VMelnalksnis/DCEL-1000/SIMULATION/LTSpice/IXTK102N65 test.asc

M1: nmos; IXTK102N65
R1: res; 2
V1: voltage; 10
V2: voltage; {gs}
Named nets: 0
.lib "D:\\projects\\Electronic-Load\\SIMULATION\\LTSpice\\SPICE Models\\IXTK102N65.lib"
.step param gs list 5 6 7 8 10
.dc V1 0 25 0.1
