VMelnalksnis/DCEL-1000/SIMULATION/LTSpice/_Range Switch.asc

B1: bv; V=(white(2e7*time)/2)
B2: bv; V=(white(2e7*time)/10)
C1: cap; 470n; V=50 Rser=1m Lser=700p
L1: ind; 10n
L2: ind; 10n
L3: ind; 10n
L4: ind; 10n
L5: ind; 10m
M1: nmos; SiRC10DP
M2: nmos; SiRC10DP
Q1: npn; BC817-40
Q2: npn; BC817-40
Q3: pnp; BC807-40
R1: res; 1k
R2: res; 1k
R3: res; 100k
R4: res; 2
R5: res; 2
R6: res; 2
R7: res; 2k15
R8: res; 1.5m
R9: res; 1
V1: voltage; 12
V2: voltage; PULSE(0 5 4m 10n 10n 0.5u 100u)
V3: voltage; 20
Named nets: 0, +12V, BYP, dut+
.lib "D:\\Cloud\\OneDrive\\projects\\DCEL-1000\\SIMULATION\\LTSpice\\SPICE Models\\SiRC10DP_PS_Rev_A.LIB"
.tran 0 5.5m 5m startup uic
