VMelnalksnis/DCEL-1000/SIMULATION/LTSpice/Load Gate.asc

B1: bv; V=(white(2e6*time)/1)
B2: bv; V=(white(2e6*time)/1)
C1: cap; 10n
D1: diode; RFN30TS6D
L1: ind; {ldut}; Rser=10m
L2: ind; 100n; Rser=10m
M1: nmos; IXFX90N30
Q1: npn; BC817-25
Q2: pnp; BC807-25
Q3: pnp; BC807-25
Q4: npn; BC817-25
R1: res; 2
R2: res; 5m
R3: res; 2
R4: res; 10k
R5: res; 10k
R6: res; 10k
R7: res; 10k
R8: res; 10k
R9: res; 10k
R10: res; 10k
R11: res; 10k
R12: res; 10k
R13: res; 10k
R14: res; 5k
R15: res; 5k
R16: res; 470
U1: LT1014
U2: LT1014
U3: LT1014
V1: voltage; -15
V2: voltage; 15
V3: voltage; {vdut}; Rser={rdut}
V4: voltage; PULSE(0 5 1m 10n 10n 1m 3m)
Named nets: -15, +15, vin, 0, DUT+, DUT-, V+, V-, s, d, g
.param W=250
.param vdut=20
.param rdut=1
.param ldut=10u
.meas TRAN dv MAX abs(d(V(dut+)-V(s)))
.meas TRAN di MAX abs(d(Id(M1)))
.meas TRAN vmax MAX abs(v(dut+))
.tran 0 10m 0 startup uic
