VMelnalksnis/DCEL-1000/SIMULATION/LTSpice/Gate Buffer.asc

Q1: pnp; 2N3906
Q2: npn; 2N3904
Q3: npn; 2N3904
Q4: pnp; 2N3906
R1: res; 10k
R2: res; 10k
R3: res; 2
R4: res; 2
R5: res; 5k
R6: res; 5k
U1: LT1014
V1: voltage; SINE(2.5 2.5 20k 0 0 0)
V2: voltage; 15
V3: voltage; -15
Named nets: 0, v+, v-
.tran 0 10.5m 10m startup uic
