VMelnalksnis/DCEL-1000/SIMULATION/LTSpice/Capacitance multiplier.asc

1k5: res; 10k
C1: cap; 0.47µ; V=25 Irms=3.94 Rser=0.0265693 Lser=0 mfg="KEMET" pn="C0603C474K3PAC" type="X5R"
C2: cap; 0.47µ; V=25 Irms=3.94 Rser=0.0265693 Lser=0 mfg="KEMET" pn="C0603C474K3PAC" type="X5R"
Q1: npn; BC817-40
R1: res; 10
R3: res; 350
R4: res; 10k
V1: voltage; SINE(0 10m 200k); AC 100m
V2: voltage; 15; AC 100m
V3: voltage; SINE(0 10m 200k)
V4: voltage; 15
Named nets: 0, noise, out
.tran 0 10m 9.9m startup uic
.meas TRAN rcPP PP V(out)
.meas TRAN cmPP PP V(n002)
.meas TRAN rcAVG AVG V(out)
.meas TRAN cmAVG AVG V(n002)
.meas TRAN rcRMS RMS V(out,noise)*I(R1)
.meas TRAN cmRMS RMS V(N001,N002)*Ic(Q1)+V(N003,N002)*Ib(Q1)+V(N003,N001)*I(R3)+V(N003)*I(C2)
.meas TRAN rcATT PARAM 20*log(rcPP/0.1)
.meas TRAN cmATT PARAM 20*log(cmPP/0.1)
