VMelnalksnis/DCEL-1000/SIMULATION/LTSpice/Gate driver.asc

C1: cap; 500p
C2: cap; 0.1µ; V=16 Irms=728m Rser=0.14361 Lser=0 mfg="KEMET" pn="C0603C104K4RAC" type="X7R"
C3: cap; 500p
C4: cap; 0.1µ; V=16 Irms=728m Rser=0.14361 Lser=0 mfg="KEMET" pn="C0603C104K4RAC" type="X7R"
L1: ind; 35n
L2: ind; 35n
L3: ind; 35n
L4: ind; 35n
L5: ind; 35n
L6: ind; 35n
L8: ind; 50n; Rser=0
M1: nmos; SiRC10DP
M2: nmos; SiRC10DP
M3: nmos; SiRC10DP
M4: nmos; SiRC10DP
M5: nmos; SiRC10DP
M6: nmos; SiRC10DP
Q1: npn; BC817-25
Q2: npn; BC817-25
Q3: pnp; BC807-25
Q4: npn; BC817-25
Q5: npn; BC817-25
Q6: pnp; BC807-25
R1: res; 2m
R2: res; 1k
R3: res; 100k
R4: res; 1k
R5: res; 2
R6: res; 2
R7: res; 2
R8: res; 2
R9: res; 2
R10: res; 2
R11: res; 2m
R12: res; 2
R13: res; 2
R14: res; 1k
R15: res; 1k
R16: res; 100k
V1: voltage; 12; Rser=0.1
V2: voltage; PULSE(0 5 0 10n 10n 5u 10u)
V3: voltage; 10; Rser=0.1
V4: voltage; -15; Rser=0.1
V5: voltage; PULSE(0 5 10n 10n 10n 8u 10u)
Named nets: +12V, Driver_In, 0, +V, -5v, Driver_In2
.lib "D:\\Projects\\Electronic-Load\\SIMULATION\\LTSpice\\SPICE Models\\SiRC10DP_PS_Rev_A.LIB"
.tran 0 102u 87u startup uic
