VMelnalksnis/DCEL-1000/SIMULATION/LTSpice/Voltage sense.asc

R1: res; 200k; tol=1
R2: res; 200k; tol=1
R3: res; 200k; tol=1
R4: res; 200k; tol=1
R5: res; 200k; tol=1
R6: res; 200k; tol=1
R7: res; 200k; tol=1
R8: res; 200k; tol=1
R9: res; 200k; tol=1
R10: res; 200k; tol=1
R11: res; 20k
R12: res; 10k
R13: res; 10k
R14: res; 10k
R15: res; 10k
U1: OP77
V1: voltage; 15
V2: voltage; -15
V3: voltage; 800
Named nets: 0, v+, v-, out
.dc dec v3 1 650 50
