VMelnalksnis/DCEL-1000/SIMULATION/LTSpice/Bypass MOSFET.asc

M1: nmos; IPA180N10N3
M2: nmos; IPA180N10N3
M3: nmos; IPA180N10N3
R1: res; 2m
R2: res; 2
R4: res; 2k
V1: voltage; 3.3
V2: voltage; 4
V3: voltage; 10
V4: voltage; 10
Named nets: 0, Supply, Load_gate, Bypass_gate1, low, high, mid, Bypass_gate2
.dc V2 0 5 7.63e-5
