VMelnalksnis/DCEL-1000/SIMULATION/LTSpice/Opamp trimming.asc

I1: current; 50
R1: res; 4k99
R2: res; 4k99
R3: res; 200k
R4: res; 200k
R5: res; 200
R6: res; 20k
R7: res; {rt}
R8: res; {rb}
R9: res; 2m
U2: LT1014
V1: voltage; 5
V2: voltage; -5
V3: voltage; 1m2
Named nets: V+, V-, 0
.param rt = 20k * trim
.param rb = 20k * (1-trim)
.param trim 0.154
;dc oct I1 50m 50 100
.step param trim 0.01 0.99 0.01
.op
