VMelnalksnis/DCEL-1000/SIMULATION/LTSpice/Shunts.asc

M1: nmos; BSC265N10LSF
M2: nmos; BSC265N10LSF
R1: res; 2
R3: res; 2m
U1: LT1716
V1: voltage; 600
V2: voltage; 20
V3: voltage; 20
V4: voltage; 0.2
Named nets: supply, 0, senseLow, senseHigh, senseMid
.dc dec V2 100m 10 100
